ExcessiveOverkill/POV-card-v1/STM32CubeIDE/pov-card-v2/USBX/App/app_usbx_device.c

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

/* Includes ------------------------------------------------------------------*/
#include "app_usbx_device.h"

/* USER CODE BEGIN Includes */
#include "main.h"
extern PCD_HandleTypeDef hpcd_USB_DRD_FS;
extern volatile uint8_t g_usb_connected;
extern volatile uint8_t g_usb_led_state;
extern volatile uint8_t g_bmp_pending;

/* USB diagnostic event log — each bit records that a callback ever fired.
   Read this in the debugger or display it on the LEDs.
   Bit 0  ATTACHED       bit 1  REMOVED
   Bit 2  CONNECTED      bit 3  DISCONNECTED
   Bit 4  SUSPENDED      bit 5  RESUMED
   Bit 6  SOF            bit 7  (unused)
   Bit 8  STORAGE_Activate  bit 9  STORAGE_Deactivate
   Counters saturate at 255. */
volatile uint32_t g_usb_diag_events  = 0U;   /* bitmask of callbacks fired  */
volatile uint8_t  g_usb_diag_susp_n  = 0U;   /* SUSPENDED count             */
volatile uint8_t  g_usb_diag_conn_n  = 0U;   /* CONNECTED count             */
volatile uint8_t  g_usb_diag_actv_n  = 0U;   /* STORAGE_Activate count      */
/* USER CODE END Includes */

/* USER CODE BEGIN PD */
/* UX_DEVICE_APP_MEM_POOL_SIZE and USBX_DEVICE_MEMORY_STACK_SIZE are defined
   in app_usbx_device.h without USER CODE guards, so they get regenerated to
   their defaults.  Override them here (which processes after the #include). */
#undef  UX_DEVICE_APP_MEM_POOL_SIZE
#define UX_DEVICE_APP_MEM_POOL_SIZE    3072
#undef  USBX_DEVICE_MEMORY_STACK_SIZE
#define USBX_DEVICE_MEMORY_STACK_SIZE  3072
/* USER CODE END PD */


#if defined ( __ICCARM__ )
#pragma data_alignment=4
#endif
__ALIGN_BEGIN static UCHAR ux_device_byte_pool_buffer[UX_DEVICE_APP_MEM_POOL_SIZE] __ALIGN_END;

static ULONG storage_interface_number;
static ULONG storage_configuration_number;
static UX_SLAVE_CLASS_STORAGE_PARAMETER storage_parameter;

static UINT USBD_ChangeFunction(ULONG Device_State);
/**
  * @brief  Application USBX Device Initialization.
  * @param  none
  * @retval status
  */

UINT MX_USBX_Device_Init(VOID)
{
   UINT ret = UX_SUCCESS;
  UCHAR *device_framework_high_speed;
  UCHAR *device_framework_full_speed;
  ULONG device_framework_hs_length;
  ULONG device_framework_fs_length;
  ULONG string_framework_length;
  ULONG language_id_framework_length;
  UCHAR *string_framework;
  UCHAR *language_id_framework;

  UCHAR *pointer;

  pointer = ux_device_byte_pool_buffer;

  /* Initialize USBX Memory */
  if (ux_system_initialize(pointer, USBX_DEVICE_MEMORY_STACK_SIZE, UX_NULL, 0) != UX_SUCCESS)
  {
    /* USER CODE BEGIN USBX_SYSTEM_INITIALIZE_ERROR */
    return UX_ERROR;
    /* USER CODE END USBX_SYSTEM_INITIALIZE_ERROR */
  }

  /* Get Device Framework High Speed and get the length */
  device_framework_high_speed = USBD_Get_Device_Framework_Speed(USBD_HIGH_SPEED,
                                                                &device_framework_hs_length);

  /* Get Device Framework Full Speed and get the length */
  device_framework_full_speed = USBD_Get_Device_Framework_Speed(USBD_FULL_SPEED,
                                                                &device_framework_fs_length);

  /* Get String Framework and get the length */
  string_framework = USBD_Get_String_Framework(&string_framework_length);

  /* Get Language Id Framework and get the length */
  language_id_framework = USBD_Get_Language_Id_Framework(&language_id_framework_length);

  /* Install the device portion of USBX */
  if (ux_device_stack_initialize(device_framework_high_speed,
                                 device_framework_hs_length,
                                 device_framework_full_speed,
                                 device_framework_fs_length,
                                 string_framework,
                                 string_framework_length,
                                 language_id_framework,
                                 language_id_framework_length,
                                 USBD_ChangeFunction) != UX_SUCCESS)
  {
    /* USER CODE BEGIN USBX_DEVICE_INITIALIZE_ERROR */
    return UX_ERROR;
    /* USER CODE END USBX_DEVICE_INITIALIZE_ERROR */
  }

  /* Initialize the storage class parameters for the device */
  storage_parameter.ux_slave_class_storage_instance_activate   = USBD_STORAGE_Activate;
  storage_parameter.ux_slave_class_storage_instance_deactivate = USBD_STORAGE_Deactivate;

  /* Store the number of LUN in this device storage instance */
  storage_parameter.ux_slave_class_storage_parameter_number_lun = STORAGE_NUMBER_LUN;

  /* Initialize the storage class parameters for reading/writing to the Flash Disk */
  storage_parameter.ux_slave_class_storage_parameter_lun[0].
    ux_slave_class_storage_media_last_lba = USBD_STORAGE_GetMediaLastLba();

  storage_parameter.ux_slave_class_storage_parameter_lun[0].
    ux_slave_class_storage_media_block_length = USBD_STORAGE_GetMediaBlocklength();

  storage_parameter.ux_slave_class_storage_parameter_lun[0].
    ux_slave_class_storage_media_type = 0;

  storage_parameter.ux_slave_class_storage_parameter_lun[0].
    ux_slave_class_storage_media_removable_flag = STORAGE_REMOVABLE_FLAG;

  storage_parameter.ux_slave_class_storage_parameter_lun[0].
    ux_slave_class_storage_media_read_only_flag = STORAGE_READ_ONLY;

  storage_parameter.ux_slave_class_storage_parameter_lun[0].
    ux_slave_class_storage_media_read = USBD_STORAGE_Read;

  storage_parameter.ux_slave_class_storage_parameter_lun[0].
    ux_slave_class_storage_media_write = USBD_STORAGE_Write;

  storage_parameter.ux_slave_class_storage_parameter_lun[0].
    ux_slave_class_storage_media_flush = USBD_STORAGE_Flush;

  storage_parameter.ux_slave_class_storage_parameter_lun[0].
    ux_slave_class_storage_media_status = USBD_STORAGE_Status;

  storage_parameter.ux_slave_class_storage_parameter_lun[0].
    ux_slave_class_storage_media_notification = USBD_STORAGE_Notification;

  /* Get storage configuration number */
  storage_configuration_number = USBD_Get_Configuration_Number(CLASS_TYPE_MSC, 0);

  /* Find storage interface number */
  storage_interface_number = USBD_Get_Interface_Number(CLASS_TYPE_MSC, 0);

  /* Initialize the device storage class */
  if (ux_device_stack_class_register(_ux_system_slave_class_storage_name,
                                     ux_device_class_storage_entry,
                                     storage_configuration_number,
                                     storage_interface_number,
                                     &storage_parameter) != UX_SUCCESS)
  {
    /* USER CODE BEGIN USBX_DEVICE_STORAGE_REGISTER_ERROR */
    return UX_ERROR;
    /* USER CODE END USBX_DEVICE_STORAGE_REGISTER_ERROR */
  }

  /* USER CODE BEGIN MX_USBX_Device_Init1 */

  /* Connect the STM32 HAL PCD driver to the USBX device controller */
  if (ux_dcd_stm32_initialize((ULONG)USB_DRD_FS, (ULONG)&hpcd_USB_DRD_FS) != UX_SUCCESS)
    return UX_ERROR;

  /* Start USB hardware — begins enumeration on the bus */
  HAL_PCD_Start(&hpcd_USB_DRD_FS);

  /* USER CODE END MX_USBX_Device_Init1 */

  return ret;
}

/**
  * @brief  _ux_utility_interrupt_disable
  *         USB utility interrupt disable.
  * @param  none
  * @retval none
  */
ALIGN_TYPE _ux_utility_interrupt_disable(VOID)
{
  UINT interrupt_save;
  /* USER CODE BEGIN _ux_utility_interrupt_disable */
  interrupt_save = __get_PRIMASK();
  __disable_irq();
  /* USER CODE END _ux_utility_interrupt_disable */

  return interrupt_save;
}

/**
  * @brief  _ux_utility_interrupt_restore
  *         USB utility interrupt restore.
  * @param  flags
  * @retval none
  */
VOID _ux_utility_interrupt_restore(ALIGN_TYPE flags)
{

  /* USER CODE BEGIN _ux_utility_interrupt_restore */
  __set_PRIMASK(flags);
  /* USER CODE END _ux_utility_interrupt_restore */
}

/**
  * @brief  _ux_utility_time_get
  *         Get Time Tick for host timing.
  * @param  none
  * @retval time tick
  */
ULONG _ux_utility_time_get(VOID)
{
  ULONG time_tick = 0U;

  /* USER CODE BEGIN _ux_utility_time_get */
  time_tick = (ULONG)HAL_GetTick();
  /* USER CODE END _ux_utility_time_get */

  return time_tick;
}

/**
  * @brief  USBD_ChangeFunction
  *         This function is called when the device state changes.
  * @param  Device_State: USB Device State
  * @retval status
  */
static UINT USBD_ChangeFunction(ULONG Device_State)
{
   UINT status = UX_SUCCESS;

  switch (Device_State)
  {
    case UX_DEVICE_ATTACHED:

      /* USER CODE BEGIN UX_DEVICE_ATTACHED */
      /* Fires on every bus reset (start of enumeration). With
         vbus_sensing_enable=DISABLE, HAL_PCD_ConnectCallback never runs, so
         UX_DCD_STM32_DEVICE_CONNECTED is dead -- this is our connect signal. */
      g_usb_diag_events |= (1U << 0);
      g_usb_connected = 1U;
      /* USER CODE END UX_DEVICE_ATTACHED */

      break;

    case UX_DEVICE_REMOVED:

      /* USER CODE BEGIN UX_DEVICE_REMOVED */
      g_usb_diag_events |= (1U << 1);
      g_usb_connected = 0U;
      /* USER CODE END UX_DEVICE_REMOVED */

      break;

    case UX_DCD_STM32_DEVICE_CONNECTED:

      /* USER CODE BEGIN UX_DCD_STM32_DEVICE_CONNECTED */
      g_usb_diag_events |= (1U << 2);
      if (g_usb_diag_conn_n < 255U) g_usb_diag_conn_n++;
      g_usb_connected = 1U;
      g_usb_led_state = 1U;
      /* USER CODE END UX_DCD_STM32_DEVICE_CONNECTED */

      break;

    case UX_DCD_STM32_DEVICE_DISCONNECTED:

      /* USER CODE BEGIN UX_DCD_STM32_DEVICE_DISCONNECTED */
      g_usb_diag_events |= (1U << 3);
      g_usb_connected = 0U;
      g_usb_led_state = 0U;
      /* USER CODE END UX_DCD_STM32_DEVICE_DISCONNECTED */

      break;

    case UX_DCD_STM32_DEVICE_SUSPENDED:

      /* USER CODE BEGIN UX_DCD_STM32_DEVICE_SUSPENDED */
      g_usb_diag_events |= (1U << 4);
      if (g_usb_diag_susp_n < 255U) g_usb_diag_susp_n++;
      g_usb_connected = 0U;
      g_usb_led_state = 0U;
      g_bmp_pending   = 0U;
      /* USER CODE END UX_DCD_STM32_DEVICE_SUSPENDED */

      break;

    case UX_DCD_STM32_DEVICE_RESUMED:

      /* USER CODE BEGIN UX_DCD_STM32_DEVICE_RESUMED */
      g_usb_diag_events |= (1U << 5);
      g_usb_connected = 1U;    /* host came back after a suspend */
      /* USER CODE END UX_DCD_STM32_DEVICE_RESUMED */

      break;

    case UX_DCD_STM32_SOF_RECEIVED:

      break;

    default:

      break;

  }

  return status;
}
